xx20170204xx/ArduinoCarDriveLoger/Fig/Arduino/IMG_20220725_015618122.png

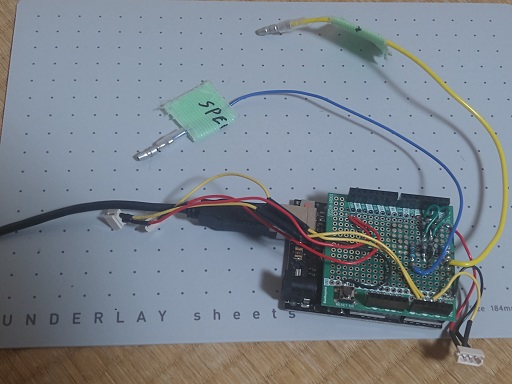
Fig/Arduino/IMG_20220725_015618122.png
