xx20170204xx/ArduinoCarDriveLoger/Fig/UnityClient/20220802.png

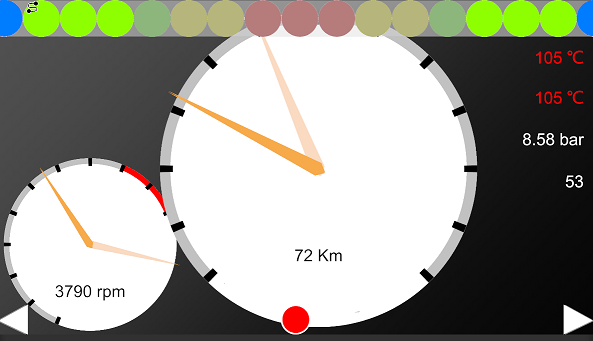
Fig/UnityClient/20220802.png
